selva-ragaavan/AVIONIX-28/Avionix-28_Pcbfiles/Avionix-28_Pcbfiles.kicad_sch

## KiCad design Avionix-28_Pcbfiles/Avionix-28_Pcbfiles.kicad_sch (2026-09-07)

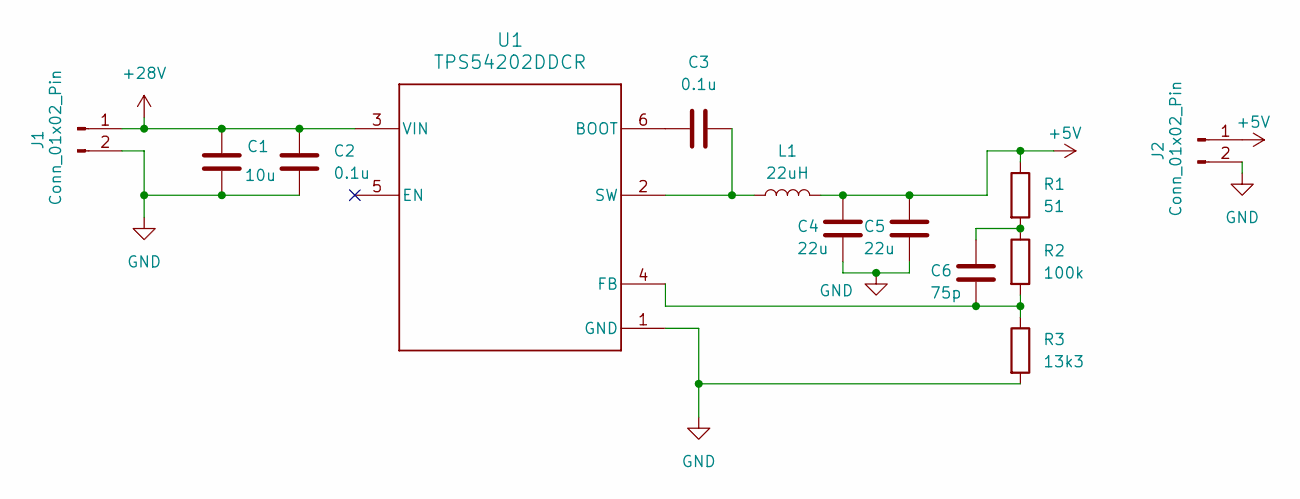
[picture p3: schematic Avionix-28_Pcbfiles.kicad_sch]

Parts:
C1: 10u; C_1210_3225Metric
C2, C3: 0.1u; C_0402_1005Metric
C4, C5: 22u; C_1210_3225Metric
C6: 75p; C_0805_2012Metric
J1, J2: Conn_01x02_Pin; Connector_PinHeader_3.81
L1: 22uH; IND_CD54_SUM
R1: 51; R_0805_2012Metric
R2: 100k; R_0805_2012Metric
R3: 13k3; R_0805_2012Metric
U1: TPS54202DDCR; DDC0006A_N

Connections:
+5V: C4.2, C5.2, J2.1, L1.2, R1.1
+28V: C1.1, C2.1, J1.1, U1.3 (VIN)
GND: C1.2, C2.2, C4.1, C5.1, J1.2, J2.2, R3.2, U1.1 (GND)
unnamed: C3.1, U1.6 (BOOT)
unnamed: C3.2, L1.1, U1.2 (SW)
unnamed: C6.1, R2.2, R3.1, U1.4 (FB)
unnamed: C6.2, R1.2, R2.1
