selva-ragaavan/AVIONIX-28/Avionix-28_Pcbfiles/_restore_backup_2026-08-23T18-25-53-473/Avionix-28_Pcbfiles.kicad_sch

## KiCad design Avionix-28_Pcbfiles/_restore_backup_2026-08-23T18-25-53-473/Avionix-28_Pcbfiles.kicad_sch (2026-08-20)

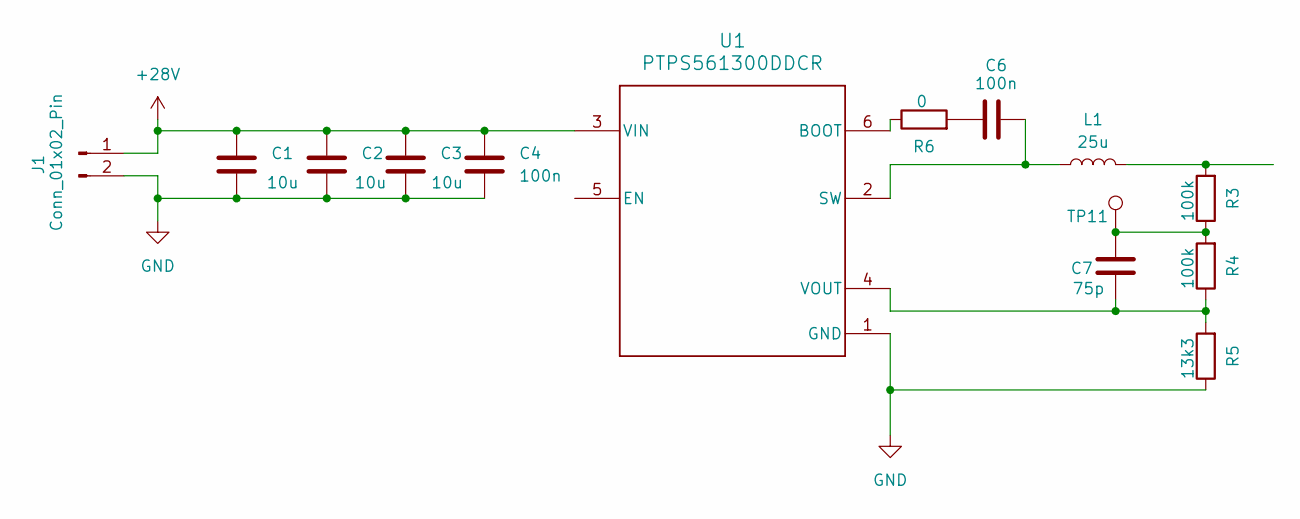
[picture p4: schematic Avionix-28_Pcbfiles.kicad_sch]

Parts:
C1, C2, C3: 10u
C4, C6: 100n
C7: 75p
J1: Conn_01x02_Pin; CUI_TB007-508-02BE
L1: 25u
R3, R4: 100k
R5: 13k3
R6: 0
TP11: TestPoint
U1: PTPS561300DDCR; DDC0006A-IPC_A

Connections:
+28V: C1.1, C2.1, C3.1, C4.1, J1.1, U1.3 (VIN)
GND: C1.2, C2.2, C3.2, C4.2, J1.2, R5.1, U1.1 (GND)
unnamed: C6.1, R6.2
unnamed: C6.2, L1.1, U1.2 (SW)
unnamed: C7.1, R4.1, R5.2, U1.4 (VOUT)
unnamed: C7.2, R3.1, R4.2, TP11.1
unnamed: L1.2, R3.2
unnamed: R6.1, U1.6 (BOOT)
